Egank2/Snowboard-Wearable/hardware/electrical/Snowboard-Recorder-PCB/models/MCP73831T-2ACI_OT.step

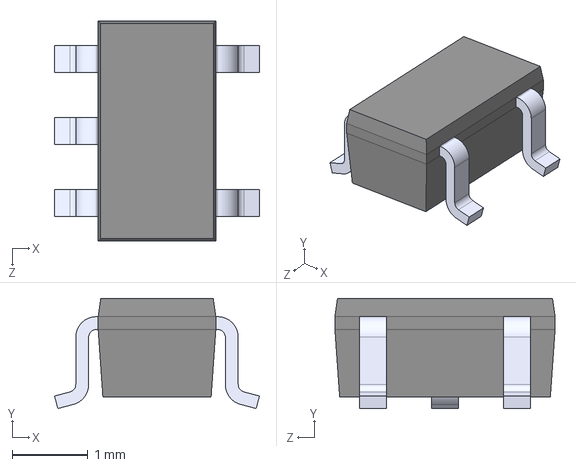
[picture p24: CAD file, 2025-04-12]
hardware/electrical/Snowboard-Recorder-PCB/models/MCP73831T-2ACI_OT.step
2.70 x 1.45 x 2.90 mm
