Egank2/Snowboard-Wearable/hardware/software/snowtrack/main/spp_server.c

#include <stdint.h>
#include <string.h>
#include <stdbool.h>
#include <stdio.h>
#include <inttypes.h>
#include "nvs.h"
#include "nvs_flash.h"
#include "freertos/FreeRTOS.h"
#include "freertos/task.h"
#include "esp_log.h"
#include "esp_bt.h"
#include "esp_bt_main.h"
#include "esp_gap_bt_api.h"
#include "esp_bt_device.h"
#include "esp_spp_api.h"
#include "sh2.h"
#include <math.h>
#include "bno08x.h"
#include "sdkconfig.h"
#include "bno08x.h"
#include "spp_server.h"

#include "time.h"
#include "sys/time.h"


#define DEG_TO_RAD 0.017453292519943295769236907684886
#define RAD_TO_DEG 57.295779513082320876798154814105

// #define SPP_TAG 
#define SPP_SERVER_NAME "SPP_SERVER"
#define SPP_SHOW_DATA 0
#define SPP_SHOW_SPEED 1
#define SPP_SHOW_MODE SPP_SHOW_DATA    /*Choose show mode: show data or speed*/

#define SQ(x) (x * x)

typedef enum {
    TYPE_START_RECORDING     = 0x01,
    TYPE_STOP_RECORDING      = 0x02,
    TYPE_RECEIVE_RECORDINGS  = 0x03,
    TYPE_CLEAR_RECORDINGS    = 0x04
} command_type_t;

typedef enum {
    RESP_STATUS
} response_type_t;

enum status_t {
    STAT_OK,
    STAT_INVALID_COMMAND,
    STAT_COMMAND_QUEUE_FULL,
    STAT_ERROR
};

typedef struct {
    command_type_t command_type;
    uint8_t params[10];
} command_t;

static const char *TAG = "SPP_SERVER";
static const char local_device_name[] = CONFIG_EXAMPLE_LOCAL_DEVICE_NAME;
static const esp_spp_mode_t esp_spp_mode = ESP_SPP_MODE_CB;
static const bool esp_spp_enable_l2cap_ertm = true;

static struct timeval time_new, time_old;
static long data_num = 0;

static const esp_spp_sec_t sec_mask = ESP_SPP_SEC_NONE;
static const esp_spp_role_t role_slave = ESP_SPP_ROLE_SLAVE;

static uint32_t recent_handle = 0;

QueueHandle_t command_queue = NULL;

static char *bda2str(uint8_t * bda, char *str, size_t size)
{
    if (bda == NULL || str == NULL || size < 18) {
        return NULL;
    }

    uint8_t *p = bda;
    sprintf(str, "%02x:%02x:%02x:%02x:%02x:%02x",
            p[0], p[1], p[2], p[3], p[4], p[5]);
    return str;
}

static void esp_spp_cb(esp_spp_cb_event_t event, esp_spp_cb_param_t *param)
{
    char bda_str[18] = {0};

    switch (event) {
    case ESP_SPP_INIT_EVT:
        if (param->init.status == ESP_SPP_SUCCESS) {
            ESP_LOGI(TAG, "ESP_SPP_INIT_EVT");
            esp_spp_start_srv(sec_mask, role_slave, 0, SPP_SERVER_NAME);
        } else {
            ESP_LOGE(TAG, "ESP_SPP_INIT_EVT status:%d", param->init.status);
        }
        break;
    case ESP_SPP_DISCOVERY_COMP_EVT:
        ESP_LOGI(TAG, "ESP_SPP_DISCOVERY_COMP_EVT");
        break;
    case ESP_SPP_OPEN_EVT:
        ESP_LOGI(TAG, "ESP_SPP_OPEN_EVT");
        break;
    case ESP_SPP_CLOSE_EVT:
        ESP_LOGI(TAG, "ESP_SPP_CLOSE_EVT status:%d handle:%"PRIu32" close_by_remote:%d", param->close.status,
                 param->close.handle, param->close.async);
        recent_handle = 0;
        break;
    case ESP_SPP_START_EVT:
        if (param->start.status == ESP_SPP_SUCCESS) {
            ESP_LOGI(TAG, "ESP_SPP_START_EVT handle:%"PRIu32" sec_id:%d scn:%d", param->start.handle, param->start.sec_id,
                     param->start.scn);
            esp_bt_gap_set_device_name(local_device_name);
            esp_bt_gap_set_scan_mode(ESP_BT_CONNECTABLE, ESP_BT_GENERAL_DISCOVERABLE);
        } else {
            ESP_LOGE(TAG, "ESP_SPP_START_EVT status:%d", param->start.status);
        }
        break;
    case ESP_SPP_CL_INIT_EVT:
        ESP_LOGI(TAG, "ESP_SPP_CL_INIT_EVT");
        break;
    case ESP_SPP_DATA_IND_EVT:
    {
        ESP_LOGI(TAG, "ESP_SPP_DATA_IND_EVT len:%d handle:%"PRIu32, param->data_ind.len, param->data_ind.handle);
        if (param->data_ind.len < 128) {
            ESP_LOG_BUFFER_CHAR(TAG, param->data_ind.data, param->data_ind.len);
        }

        // Queue command
        if (command_queue != NULL) {
            command_t command = {
                .command_type = param->data_ind.data[0]
            };

            // Catch invalid commands
            if (command.command_type > TYPE_CLEAR_RECORDINGS) {
                uint8_t response[2] = {RESP_STATUS, STAT_INVALID_COMMAND};
                esp_spp_write(recent_handle, sizeof(response), response);
                break;
            }

            BaseType_t rtos_ret = xQueueSend(command_queue, &command, pdMS_TO_TICKS(100));

            // Check queue ret
            if (rtos_ret == errQUEUE_FULL) {
                ESP_LOGE(TAG, "Couldn't queue command because command queue is full");
                uint8_t response[2] = {RESP_STATUS, STAT_COMMAND_QUEUE_FULL};
                esp_spp_write(recent_handle, sizeof(response), response);
                break;
            } else if (rtos_ret != pdPASS) {
                ESP_LOGE(TAG, "Couldn't queue command (%d)", rtos_ret);
                break;
            }
        }
    }
        break;
    case ESP_SPP_CONG_EVT:
        ESP_LOGI(TAG, "ESP_SPP_CONG_EVT");
        break;
    case ESP_SPP_WRITE_EVT:
        ESP_LOGI(TAG, "ESP_SPP_WRITE_EVT");
        break;
    case ESP_SPP_SRV_OPEN_EVT:
        ESP_LOGI(TAG, "ESP_SPP_SRV_OPEN_EVT status:%d handle:%"PRIu32", rem_bda:[%s]", param->srv_open.status,
                 param->srv_open.handle, bda2str(param->srv_open.rem_bda, bda_str, sizeof(bda_str)));
        gettimeofday(&time_old, NULL);
        recent_handle = param->data_ind.handle;
        break;
    case ESP_SPP_SRV_STOP_EVT:
        ESP_LOGI(TAG, "ESP_SPP_SRV_STOP_EVT");
        break;
    case ESP_SPP_UNINIT_EVT:
        ESP_LOGI(TAG, "ESP_SPP_UNINIT_EVT");
        break;
    default:
        ESP_LOGI(TAG, "EVENT: %d", event);
    }
}

void esp_bt_gap_cb(esp_bt_gap_cb_event_t event, esp_bt_gap_cb_param_t *param)
{
    char bda_str[18] = {0};

    switch (event) {
    case ESP_BT_GAP_AUTH_CMPL_EVT:{
        if (param->auth_cmpl.stat == ESP_BT_STATUS_SUCCESS) {
            ESP_LOGI(TAG, "authentication success: %s bda:[%s]", param->auth_cmpl.device_name,
                     bda2str(param->auth_cmpl.bda, bda_str, sizeof(bda_str)));
        } else {
            ESP_LOGE(TAG, "authentication failed, status:%d", param->auth_cmpl.stat);
        }
        break;
    }
    case ESP_BT_GAP_PIN_REQ_EVT:{
        ESP_LOGI(TAG, "ESP_BT_GAP_PIN_REQ_EVT min_16_digit:%d", param->pin_req.min_16_digit);
        if (param->pin_req.min_16_digit) {
            ESP_LOGI(TAG, "Input pin code: 0000 0000 0000 0000");
            esp_bt_pin_code_t pin_code = {0};
            esp_bt_gap_pin_reply(param->pin_req.bda, true, 16, pin_code);
        } else {
            ESP_LOGI(TAG, "Input pin code: 1234");
            esp_bt_pin_code_t pin_code;
            pin_code[0] = '1';
            pin_code[1] = '2';
            pin_code[2] = '3';
            pin_code[3] = '4';
            esp_bt_gap_pin_reply(param->pin_req.bda, true, 4, pin_code);
        }
        break;
    }

#if (CONFIG_EXAMPLE_SSP_ENABLED == true)
    case ESP_BT_GAP_CFM_REQ_EVT:
        ESP_LOGI(TAG, "ESP_BT_GAP_CFM_REQ_EVT Please compare the numeric value: %06"PRIu32, param->cfm_req.num_val);
        esp_bt_gap_ssp_confirm_reply(param->cfm_req.bda, true);
        break;
    case ESP_BT_GAP_KEY_NOTIF_EVT:
        ESP_LOGI(TAG, "ESP_BT_GAP_KEY_NOTIF_EVT passkey:%06"PRIu32, param->key_notif.passkey);
        break;
    case ESP_BT_GAP_KEY_REQ_EVT:
        ESP_LOGI(TAG, "ESP_BT_GAP_KEY_REQ_EVT Please enter passkey!");
        break;
#endif

    case ESP_BT_GAP_MODE_CHG_EVT:
        ESP_LOGI(TAG, "ESP_BT_GAP_MODE_CHG_EVT mode:%d bda:[%s]", param->mode_chg.mode,
                 bda2str(param->mode_chg.bda, bda_str, sizeof(bda_str)));
        break;
    default: 
            ESP_LOGI(TAG, "GAP Event: %d", event);
    }
    return;
}

void server_init() 
{
    command_queue = xQueueCreate(10, sizeof(command_t));

    esp_err_t ret;

    char bda_str[18] = {0};

    ESP_ERROR_CHECK(esp_bt_controller_mem_release(ESP_BT_MODE_BLE));

    esp_bt_controller_config_t bt_cfg = BT_CONTROLLER_INIT_CONFIG_DEFAULT();
    if ((ret = esp_bt_controller_init(&bt_cfg)) != ESP_OK) {
        ESP_LOGE(TAG, "%s initialize controller failed: %s", __func__, esp_err_to_name(ret));
        return;
    }

    if ((ret = esp_bt_controller_enable(ESP_BT_MODE_CLASSIC_BT)) != ESP_OK) {
        ESP_LOGE(TAG, "%s enable controller failed: %s", __func__, esp_err_to_name(ret));
        return;
    }

    esp_bluedroid_config_t bluedroid_cfg = BT_BLUEDROID_INIT_CONFIG_DEFAULT();
#if (CONFIG_EXAMPLE_SSP_ENABLED == false)
    bluedroid_cfg.ssp_en = false;
#endif
    if ((ret = esp_bluedroid_init_with_cfg(&bluedroid_cfg)) != ESP_OK) {
        ESP_LOGE(TAG, "%s initialize bluedroid failed: %s", __func__, esp_err_to_name(ret));
        return;
    }

    if ((ret = esp_bluedroid_enable()) != ESP_OK) {
        ESP_LOGE(TAG, "%s enable bluedroid failed: %s", __func__, esp_err_to_name(ret));
        return;
    }

    if ((ret = esp_bt_gap_register_callback(esp_bt_gap_cb)) != ESP_OK) {
        ESP_LOGE(TAG, "%s gap register failed: %s", __func__, esp_err_to_name(ret));
        return;
    }

    if ((ret = esp_spp_register_callback(esp_spp_cb)) != ESP_OK) {
        ESP_LOGE(TAG, "%s spp register failed: %s", __func__, esp_err_to_name(ret));
        return;
    }

    esp_spp_cfg_t bt_spp_cfg = {
        .mode = esp_spp_mode,
        .enable_l2cap_ertm = esp_spp_enable_l2cap_ertm,
        .tx_buffer_size = 0, /* Only used for ESP_SPP_MODE_VFS mode */
    };
    if ((ret = esp_spp_enhanced_init(&bt_spp_cfg)) != ESP_OK) {
        ESP_LOGE(TAG, "%s spp init failed: %s", __func__, esp_err_to_name(ret));
        return;
    }

#if (CONFIG_EXAMPLE_SSP_ENABLED == true)
    /* Set default parameters for Secure Simple Pairing */
    esp_bt_sp_param_t param_type = ESP_BT_SP_IOCAP_MODE;
    esp_bt_io_cap_t iocap = ESP_BT_IO_CAP_IO;
    esp_bt_gap_set_security_param(param_type, &iocap, sizeof(uint8_t));
#endif

    /*
     * Set default parameters for Legacy Pairing
     * Use variable pin, input pin code when pairing
     */
    esp_bt_pin_type_t pin_type = ESP_BT_PIN_TYPE_VARIABLE;
    esp_bt_pin_code_t pin_code;
    esp_bt_gap_set_pin(pin_type, 0, pin_code);

    ESP_LOGI(TAG, "Own address:[%s]", bda2str((uint8_t *)esp_bt_dev_get_address(), bda_str, sizeof(bda_str)));
}

void server_task(void *pvParameters)
{
    esp_log_level_set(TAG, ESP_LOG_DEBUG);
    
    server_init();

    QueueHandle_t imu_queue = NULL;
    BaseType_t rtos_ret;
    command_t command;

    UBaseType_t stack_size = uxTaskGetStackHighWaterMark(NULL);
    ESP_LOGD(TAG, "Stack size: %lu", stack_size * sizeof(configSTACK_DEPTH_TYPE));

    do {
        imu_queue = bno_get_result_queue();
        if (imu_queue == NULL) {
            vTaskDelay(50);
        }
    } while (imu_queue == NULL);

    while (1) {
        rtos_ret = xQueueReceive(command_queue, &command, portMAX_DELAY);
        if (rtos_ret != pdPASS) {
            ESP_LOGE(TAG, "Failed to recieve command from queue (%d)", rtos_ret);
            continue;
        }

        ESP_LOGI(TAG, "Task recieved command: %d", command.command_type);
    }

    vTaskDelete(NULL);
}
